dchwebb/Ball/Ball_Base_WB35/src/led.h

#pragma once
#include "initialisation.h"

class LED {
public:
	void Update();
private:
	enum class State {Off, FastFlash, SlowFlash, On, LowBattery} state {State::Off};
	void LedOn(bool on);

	uint32_t flashTimer = 0;
	uint32_t flashOn = 0;
	uint32_t flashOff = 0;
	uint32_t flashCount = 0;
	uint32_t flashUpdated = 0;
	bool lit = false;
};

extern LED led;
