dchwebb/Ball/Ball_Base_WB35/STM_Files/utilities_conf.h

#pragma once
#include "cmsis_compiler.h"
#include "string.h"

/******************************************************************************
 * common
 ******************************************************************************/
#define UTILS_ENTER_CRITICAL_SECTION( )   uint32_t primask_bit = __get_PRIMASK( );\
                                          __disable_irq( )

#define UTILS_EXIT_CRITICAL_SECTION( )          __set_PRIMASK( primask_bit )

#define UTILS_MEMSET8( dest, value, size )      memset( dest, value, size);



/******************************************************************************
 * sequencer
 * (any macro that does not need to be modified can be removed)
 ******************************************************************************/
#define UTIL_SEQ_INIT_CRITICAL_SECTION( )
#define UTIL_SEQ_ENTER_CRITICAL_SECTION( )      UTILS_ENTER_CRITICAL_SECTION( )
#define UTIL_SEQ_EXIT_CRITICAL_SECTION( )       UTILS_EXIT_CRITICAL_SECTION( )
